msafi2/ECE445-FA21-Solar/team documents/Board Schematic Draft.sch

## KiCad design team documents/Board Schematic Draft.sch (2021-10-27)

Schematic: Board Schematic Draft.sch

Parts:
C1: 1n
C2, C4, C8: 0.1u
C3, C6, C10: 47u
C5, C7, C9: 10u
D1: D_Schottky
D2, D4: LED
K1, K2: FTR-J2AK006W; RELAY_FTR-J2AK006W
ManualSwitch: Conn_01x02
OLED_Display: Conn_01x04
PCB_ScrewTerminal_3P: Conn_01x03
R1: 180k
R2, R4, R6: 10k
R3: 135k
R5: 40k
R8, R13, R16: 1k
R9: 2k
R10: 4.7k
R11, R14: 240
R12: 715
R15: 390
SW1: SW_DIP_x01
U1: ACS723xLCTR-20AU; SOIC-8_3.9x4.9mm_P1.27mm
U2: LM1117-3.3
